TimWannet/Hardware_Vocoder/Hardware/Simulation/PreAmp.asc

C1: cap; 0.01
C2: cap; 4.7µ
C3: cap; 4.7µ
D1: TVSdiode
Pot1: res2; 50K
R6: res; 2K
R7: res; 2K
R8: res; 10K
R9: res; 10K
R10: res; 1K
R11: res; 1k
R12: res; 1000000
R13: res; 150
R14: res; 150
R15: res; 68K
R16: res; 34K
U1: opamp2; opa1656
U2: opamp2; opa1656
V1: voltage; 5V
V2: voltage; -5V
XLR_2: signal; SINE(0 -2m 1K)
XLR_3: signal; SINE(0 2m 1K)
Named nets: 0
.tran {50/fs}
.inc opa1656.lib
.param fs=4kHz
XLR_1 (+GND)
Output
