TimWannet/Hardware_Vocoder/Hardware/Simulation/PreAmpV2.asc

D1: TVSdiode
R4: res; 1K
R5: res; 1K
R6: res; 10K
R7: res; 10K
R12: res; 1000000
R13: res; 150
R14: res; 150
U1: opamp2; opa1656
U2: opamp2; opa1656
U3: opamp2; opa1656
U4: opamp2; opa1656
V1: voltage; 5V
V2: voltage; -5V
XLR_2: signal; SINE(0 -2m 1K)
XLR_3: signal; SINE(0 2m 1K)
Named nets: 0
XLR_1 (+GND)
Output
.inc opa1656.lib
.param fs=4kHz
.tran {50/fs}
