TimWannet/Hardware_Vocoder/Hardware/KiCad/Main_Board/PreAmp.asc

C1: cap
C2: cap
C3: cap
D1: zener
D2: zener
D3: zener
D4: zener
Pot1: res2
R1: res
R2: res
R3: res
R4: res
R5: res
R6: res
R7: res
R8: res
R9: res
R10: res
R11: res
U1: opamp2; opa1656
U2: opamp2; opa1656
V1: voltage; 3.3V
XLR_2: signal
XLR_3: signal
Named nets: 0
.tran {5/fs}
.inc opa1656.lib
.param fs=4kHz
XLR_1 (+GND)
Output
