TimWannet/Hardware_Vocoder/Hardware/Simulation/Ina217/Ina217 Mic.asc

C1: cap; 47µF; V=63 Irms=7m Rser=1.1484 Lser=1.843n
C2: cap; 47µF; V=25 Irms=0 Rser=0.014 Lser=1000p
C3: cap; 0.1µF
C4: cap; 0.1µF
D1: diode; 1N4148
D2: diode; 1N4148
D3: diode; 1N4148
D4: diode; 1N4148
Pot: res2; 0
R1: res; 2.2K
R2: res; 2.2K
R3: res; 1Meg
R4: res; 27
R5: res; 33K
R6: res; 12K
U1: INA217
U2: opamp2; TLV2371
V1: voltage; 6V
V2: voltage; -6V
XLR_2: voltage; SINE(0 -2m 1K)
XLR_3: voltage; SINE(0 2m 1K)
Named nets: 0
.tran {50/fs}
.param fs=4kHz
.incl INA217.txt
XLR_1
.lib tlv2371.lib
